SiruiLuo/CASA0022_Spectrum_Atlas/Detector/ros_catkin_ws/src/rqt/rqt_gui/resource/rqt.png

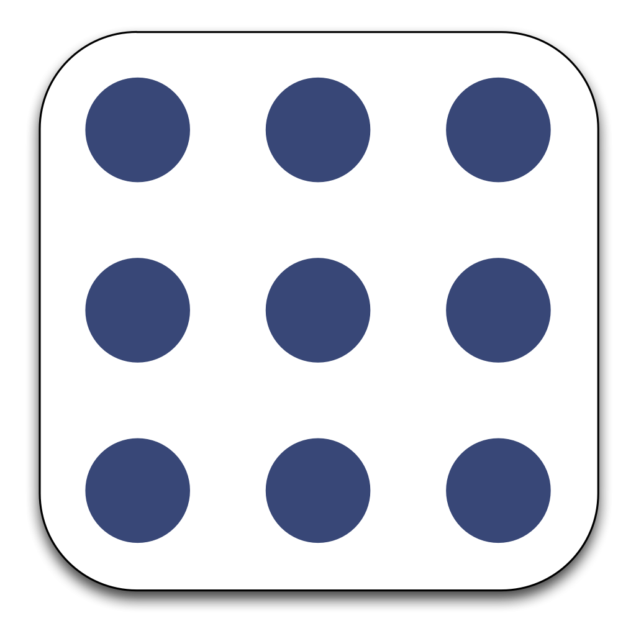
Detector/ros_catkin_ws/src/rqt/rqt_gui/resource/rqt.png
