SiruiLuo/CASA0022_Spectrum_Atlas/Detector/ros_catkin_ws/src/rqt_robot_dashboard/images/nonsvg/battery-100.png

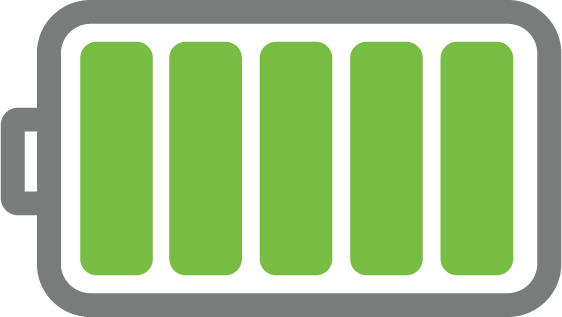
Detector/ros_catkin_ws/src/rqt_robot_dashboard/images/nonsvg/battery-100.png
