SiruiLuo/CASA0022_Spectrum_Atlas/Detector/ros_catkin_ws/src/rviz/doc/grouped-displays.png

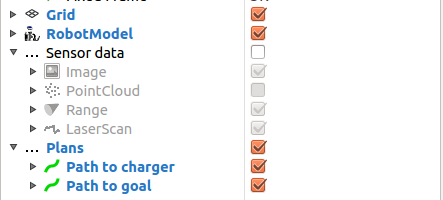
Detector/ros_catkin_ws/src/rviz/doc/grouped-displays.png
