SiruiLuo/CASA0022_Spectrum_Atlas/Detector/ros_catkin_ws/src/rviz/doc/views-panel.png

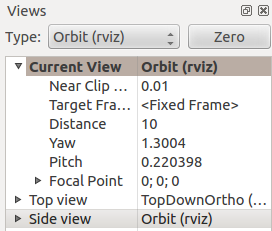
Detector/ros_catkin_ws/src/rviz/doc/views-panel.png
