SiruiLuo/CASA0022_Spectrum_Atlas/Detector/ros_catkin_ws/src/rviz/ogre_media/textures/no_image.png

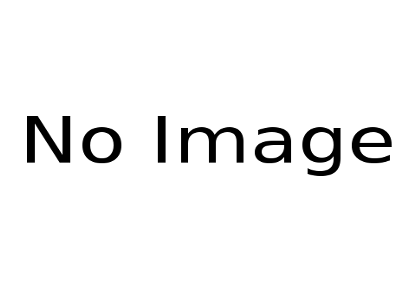
Detector/ros_catkin_ws/src/rviz/ogre_media/textures/no_image.png
