SiruiLuo/CASA0022_Spectrum_Atlas/Images/Box2.png

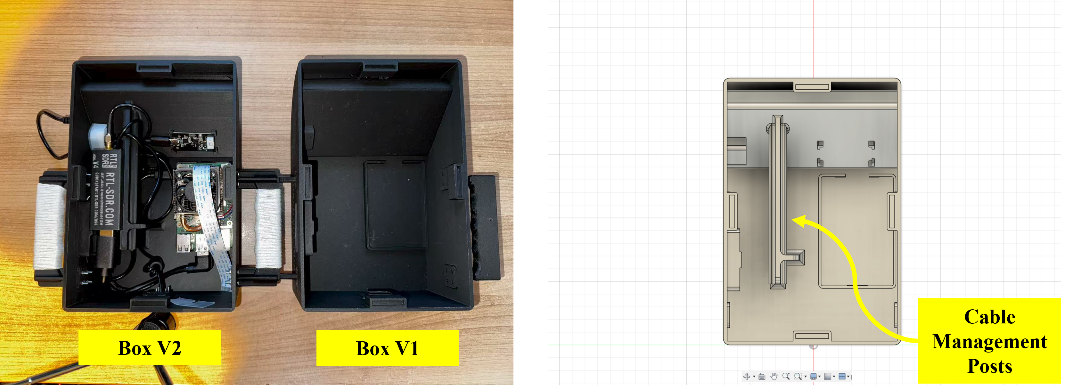
Images/Box2.png
