SiruiLuo/CASA0022_Spectrum_Atlas/Images/Cloudflare Config.png

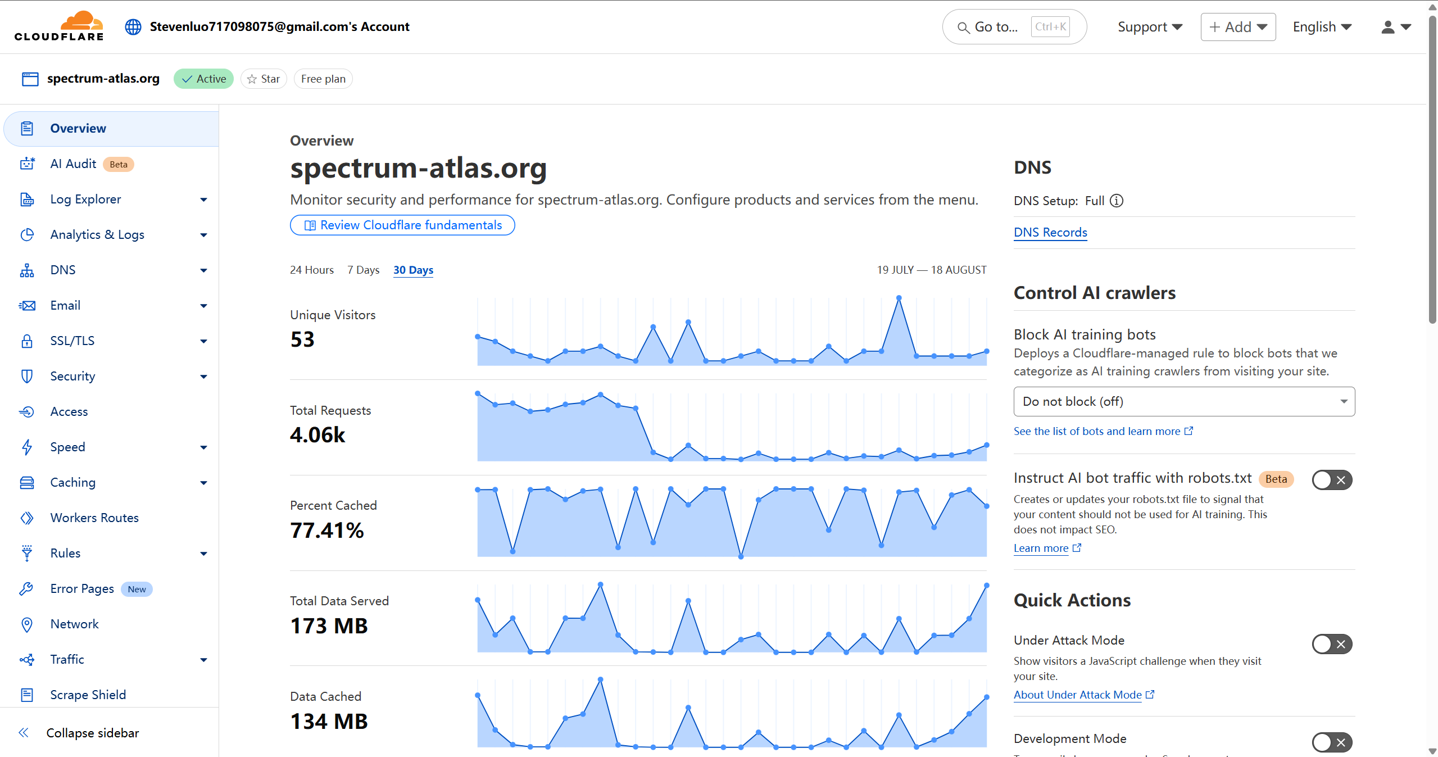
Images/Cloudflare Config.png
