SiruiLuo/CASA0022_Spectrum_Atlas/Images/Cloudflare Tunnel Settings.png

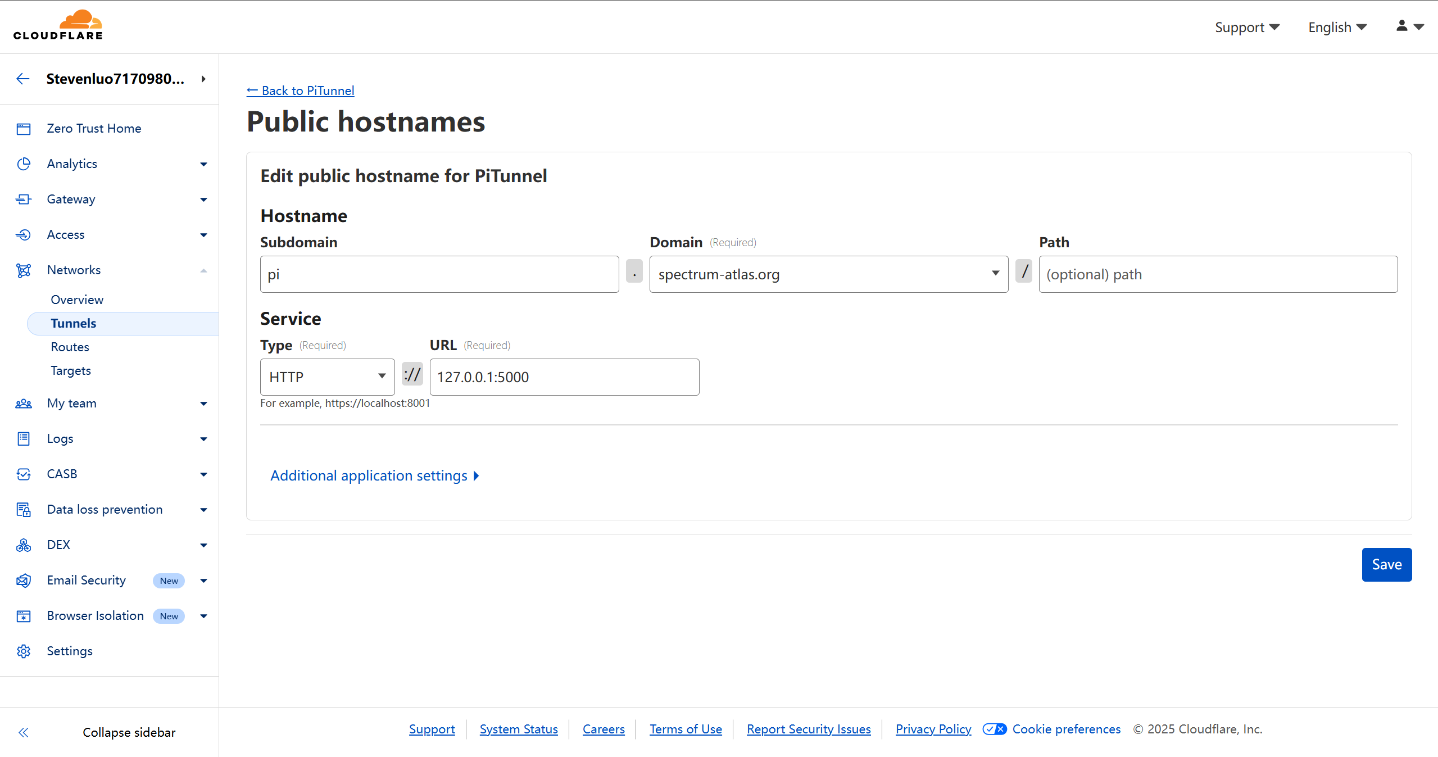
Images/Cloudflare Tunnel Settings.png
