SiruiLuo/CASA0022_Spectrum_Atlas/Images/Fan.png

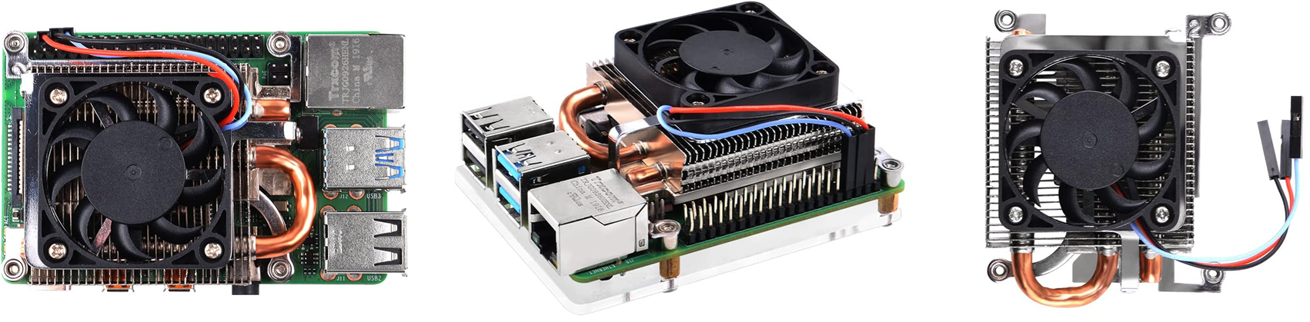
Images/Fan.png
