SiruiLuo/CASA0022_Spectrum_Atlas/Images/Flask loading.png

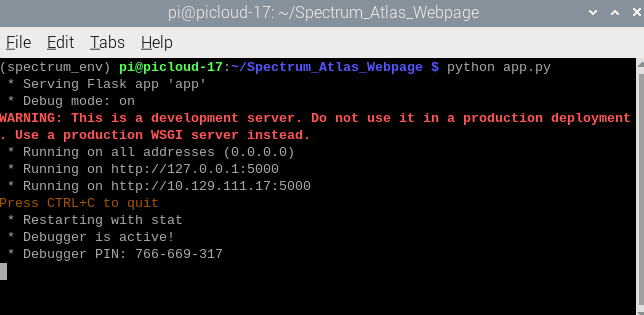
Images/Flask loading.png
