SiruiLuo/CASA0022_Spectrum_Atlas/Images/Front View.jpg

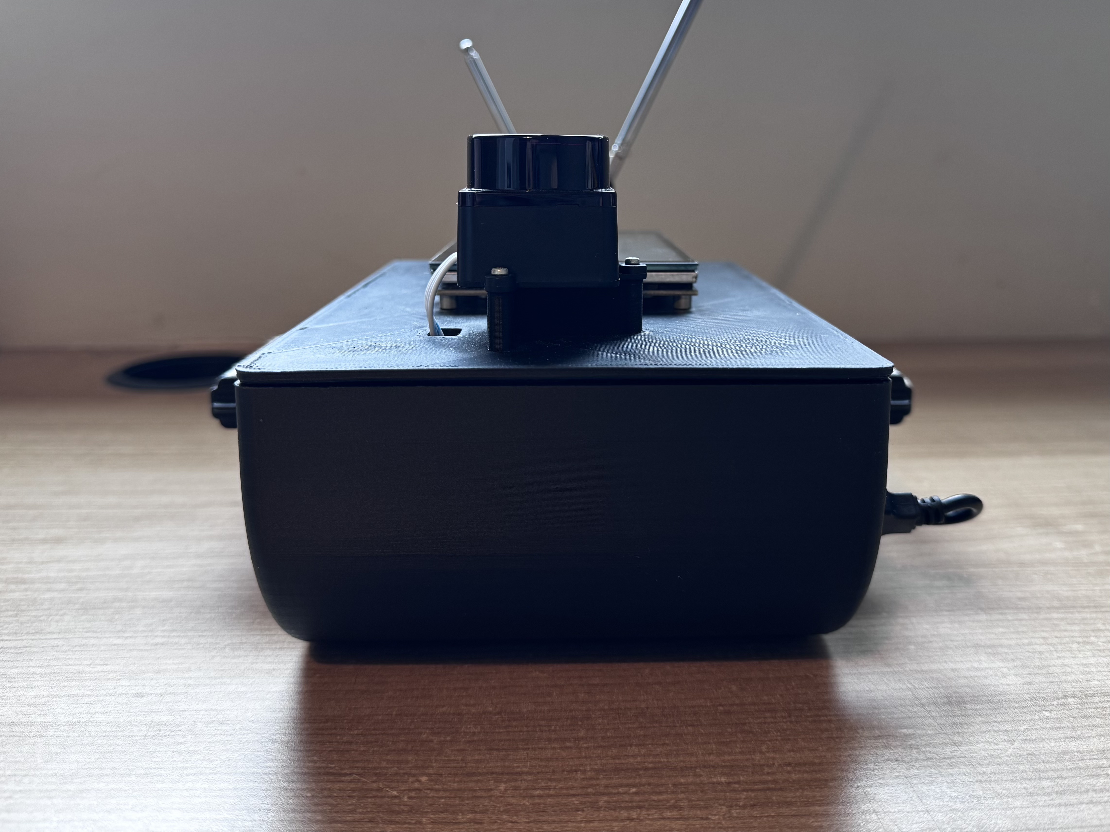
Images/Front View.jpg
