SiruiLuo/CASA0022_Spectrum_Atlas/Images/GUI flowchart.png

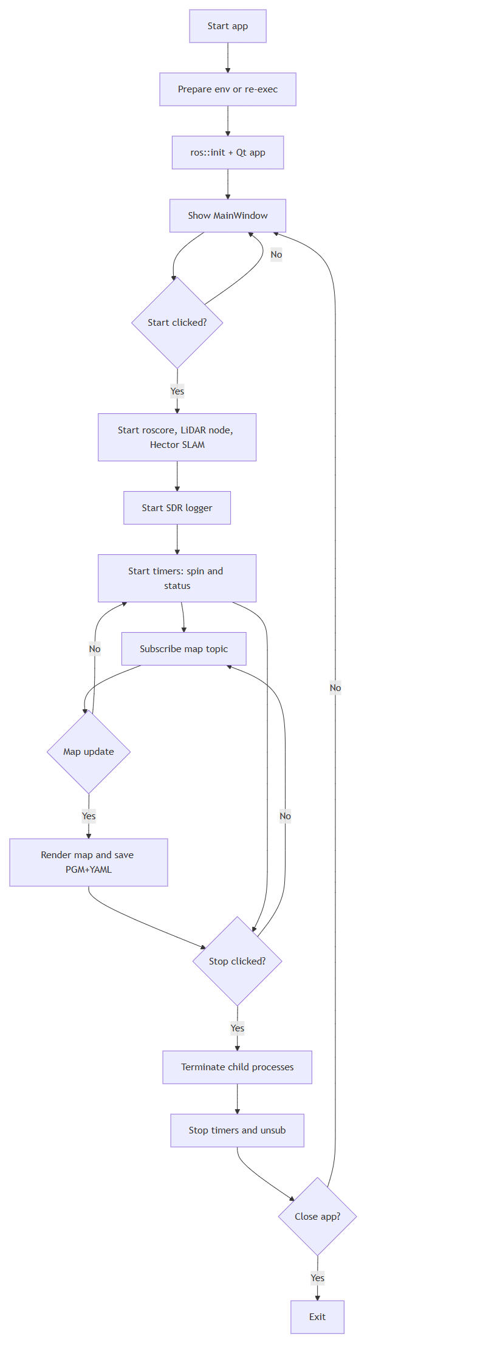
Images/GUI flowchart.png
