SiruiLuo/CASA0022_Spectrum_Atlas/Images/heatmap_ADS-B_1090_MarshgateReal_20250714_172855.png

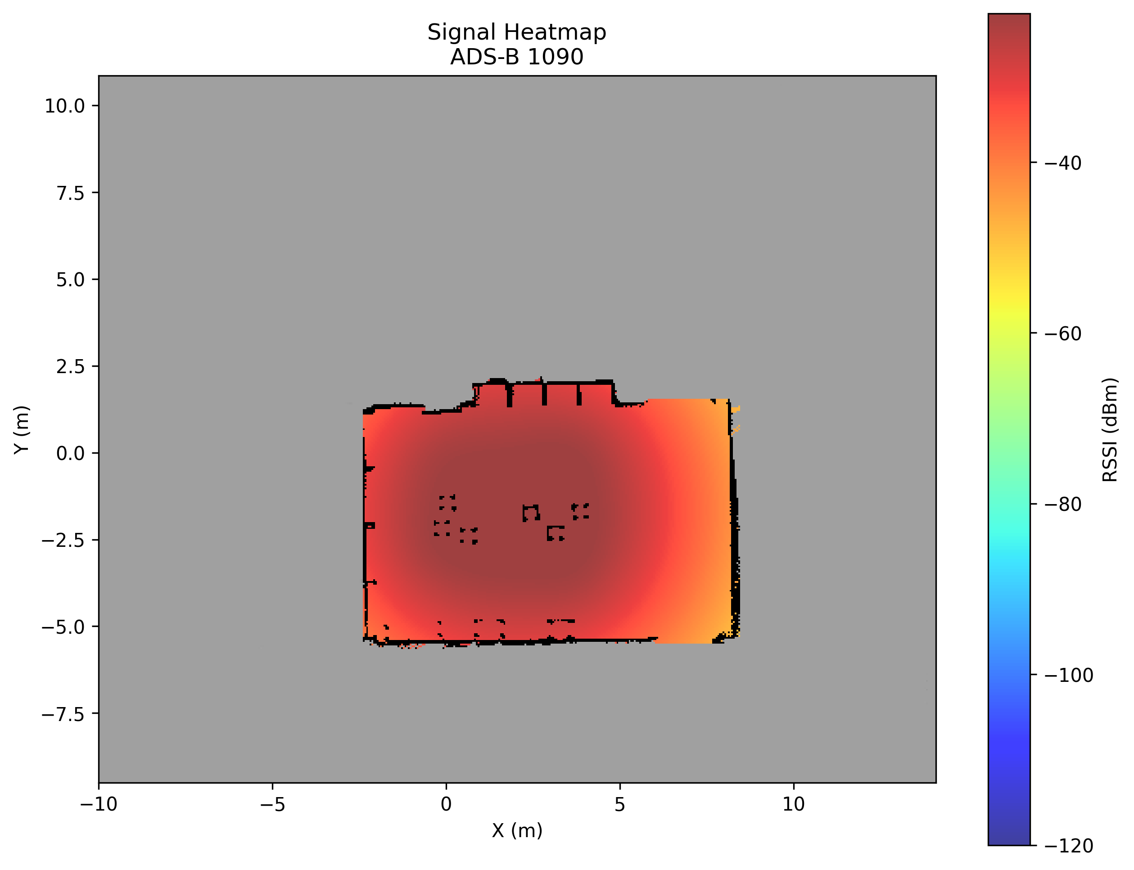
Images/heatmap_ADS-B_1090_MarshgateReal_20250714_172855.png
