SiruiLuo/CASA0022_Spectrum_Atlas/Images/Internal Overview.jpg

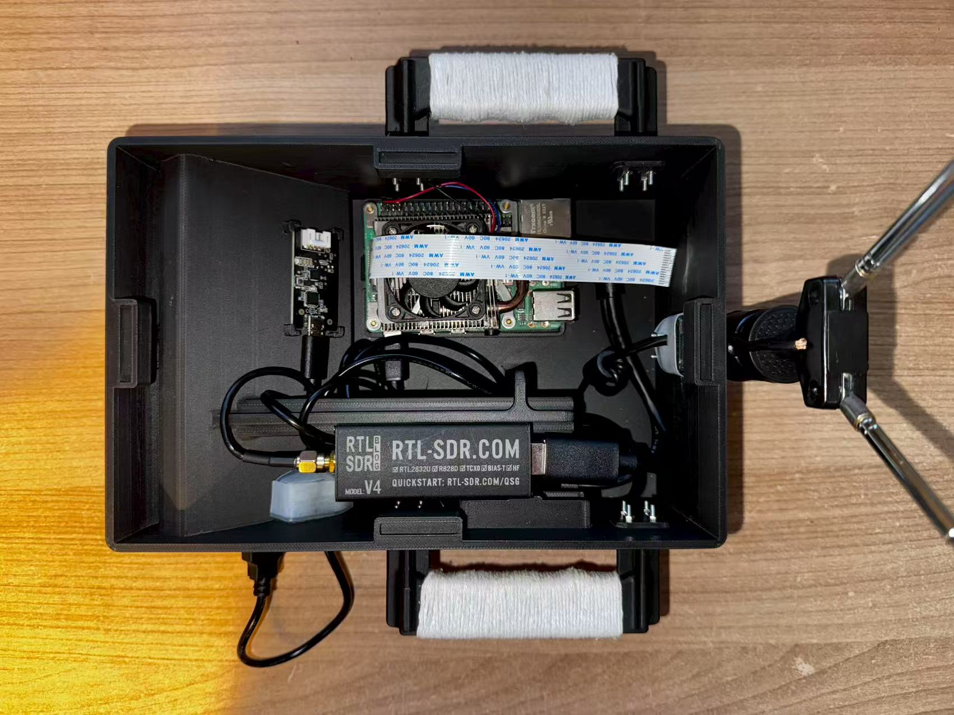
Images/Internal Overview.jpg
