SiruiLuo/CASA0022_Spectrum_Atlas/Images/LD19.png

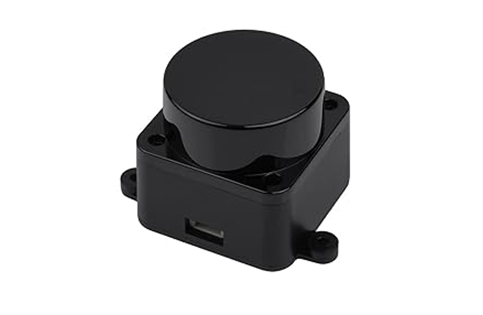
Images/LD19.png
