SiruiLuo/CASA0022_Spectrum_Atlas/Images/PostgreSQL Definition.png

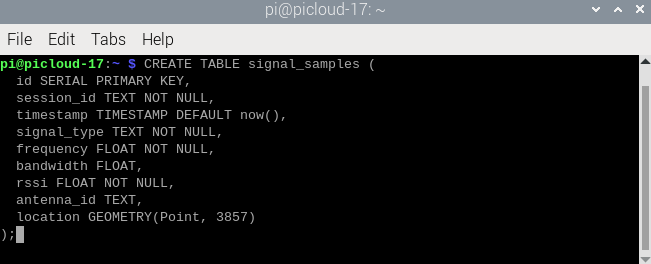
Images/PostgreSQL Definition.png
