SiruiLuo/CASA0022_Spectrum_Atlas/Images/Ringing.png

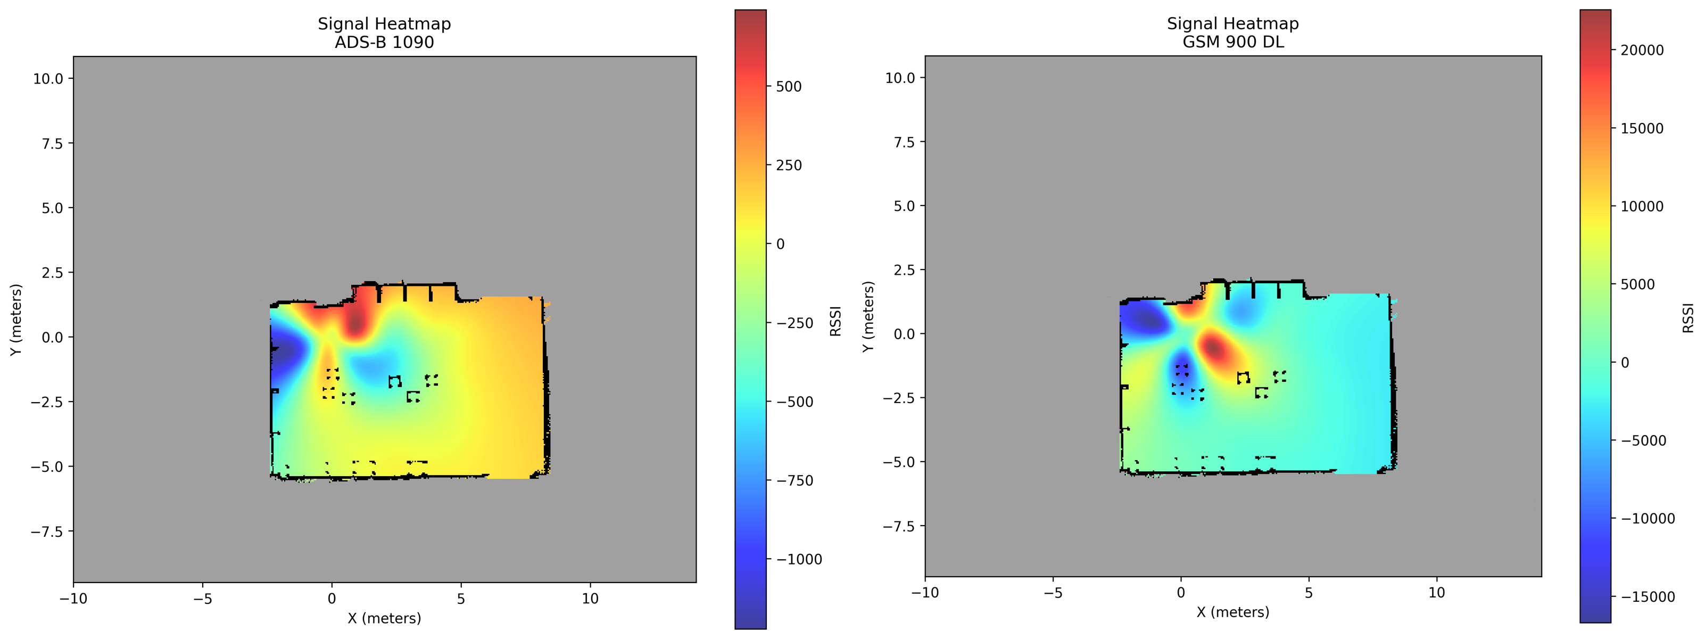
Images/Ringing.png
