SiruiLuo/CASA0022_Spectrum_Atlas/Images/RTL-SDR.png

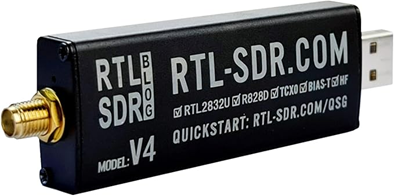
Images/RTL-SDR.png
