SiruiLuo/CASA0022_Spectrum_Atlas/Images/Side View.jpg

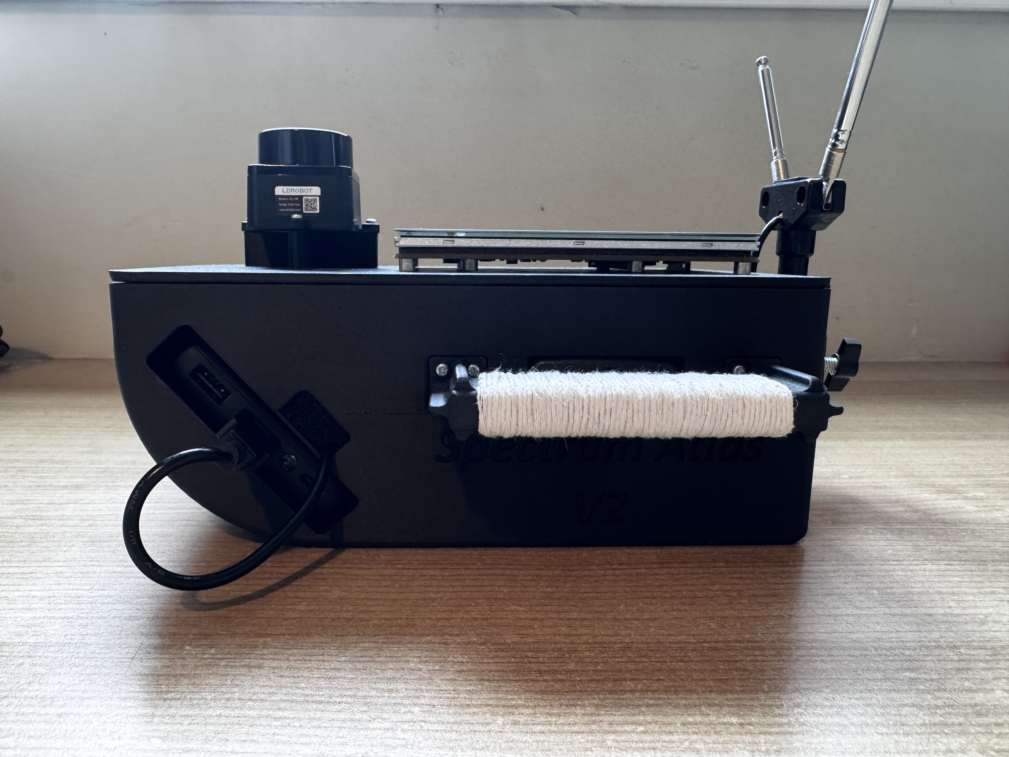
Images/Side View.jpg
