SiruiLuo/CASA0022_Spectrum_Atlas/Images/Top View.jpg

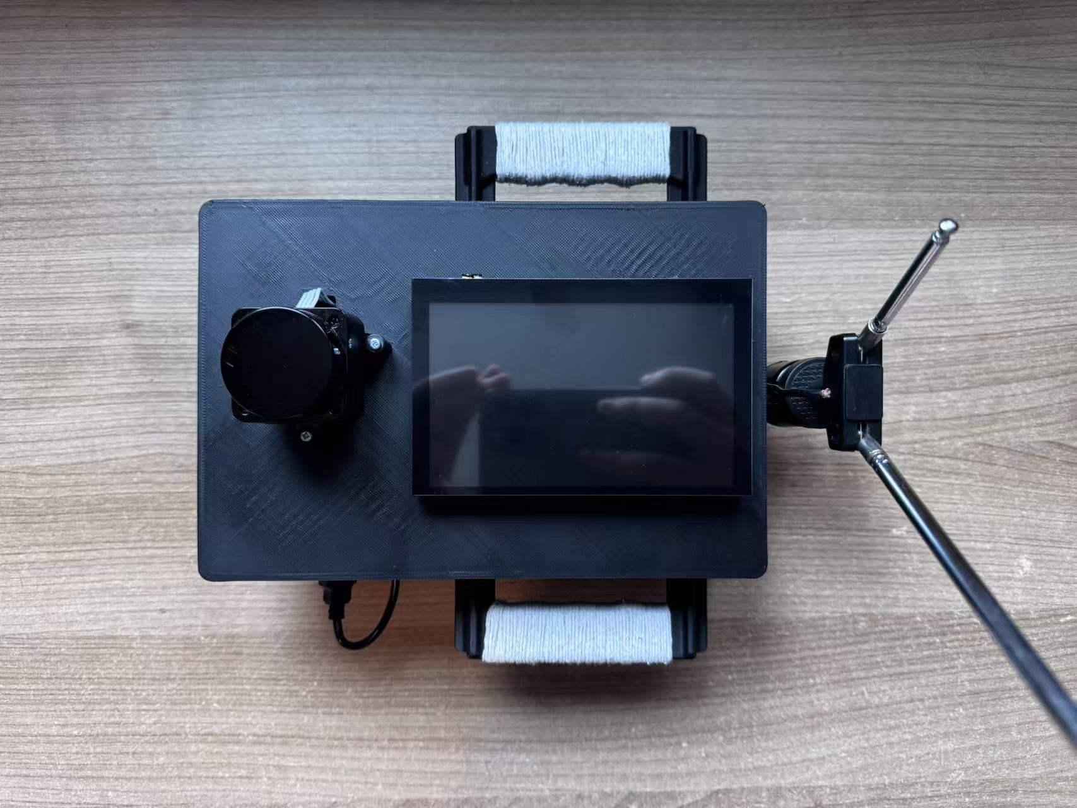
Images/Top View.jpg
