SiruiLuo/CASA0022_Spectrum_Atlas/Server and Database/Flask Server/Spectrum_Atlas_Webpage-main/pics/heat3D.png

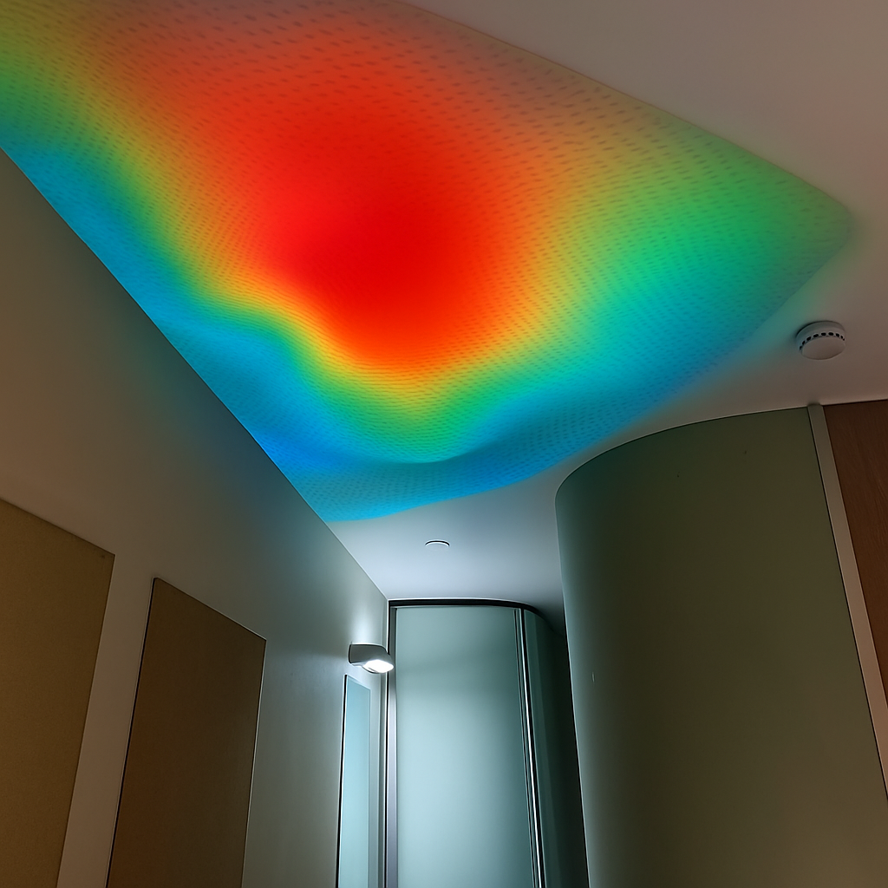
Server and Database/Flask Server/Spectrum_Atlas_Webpage-main/pics/heat3D.png
