SiruiLuo/CASA0022_Spectrum_Atlas/Server and Database/Flask Server/Spectrum_Atlas_Webpage-main/pics/Project Structure.png

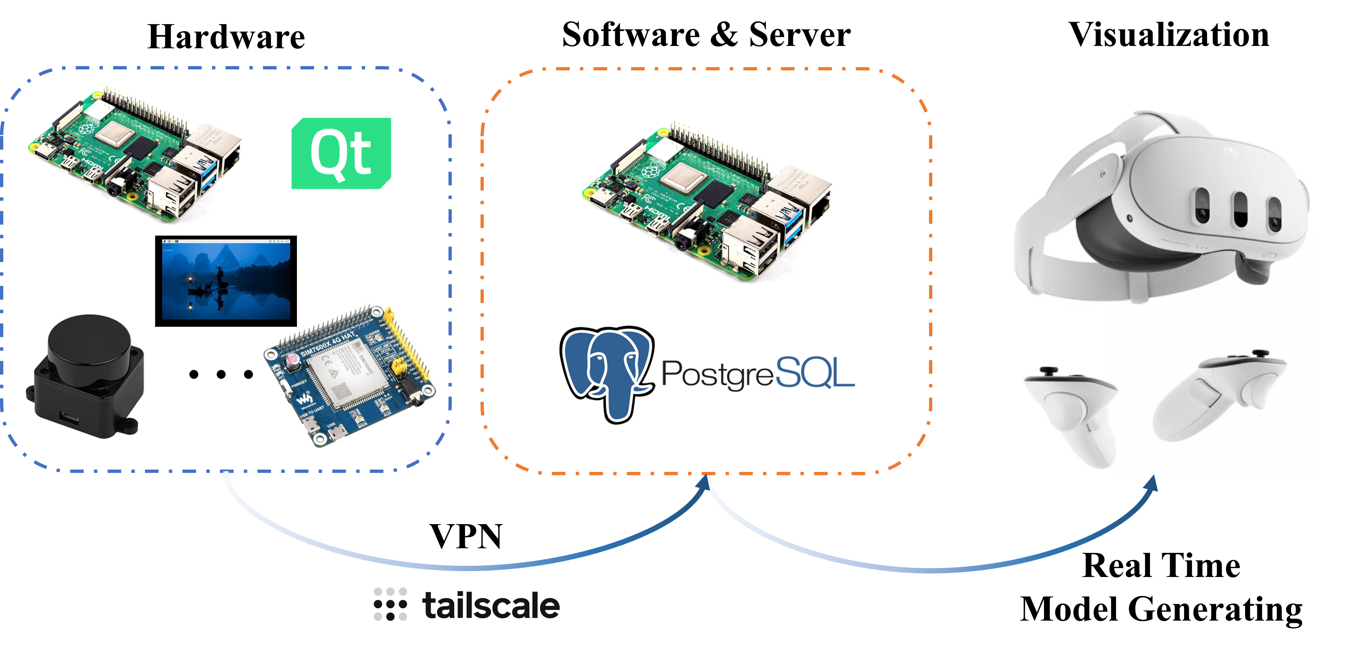
Server and Database/Flask Server/Spectrum_Atlas_Webpage-main/pics/Project Structure.png
