SiruiLuo/CASA0022_Spectrum_Atlas/Detector/ros_catkin_ws/src/urdf_tutorial/images/materials.png

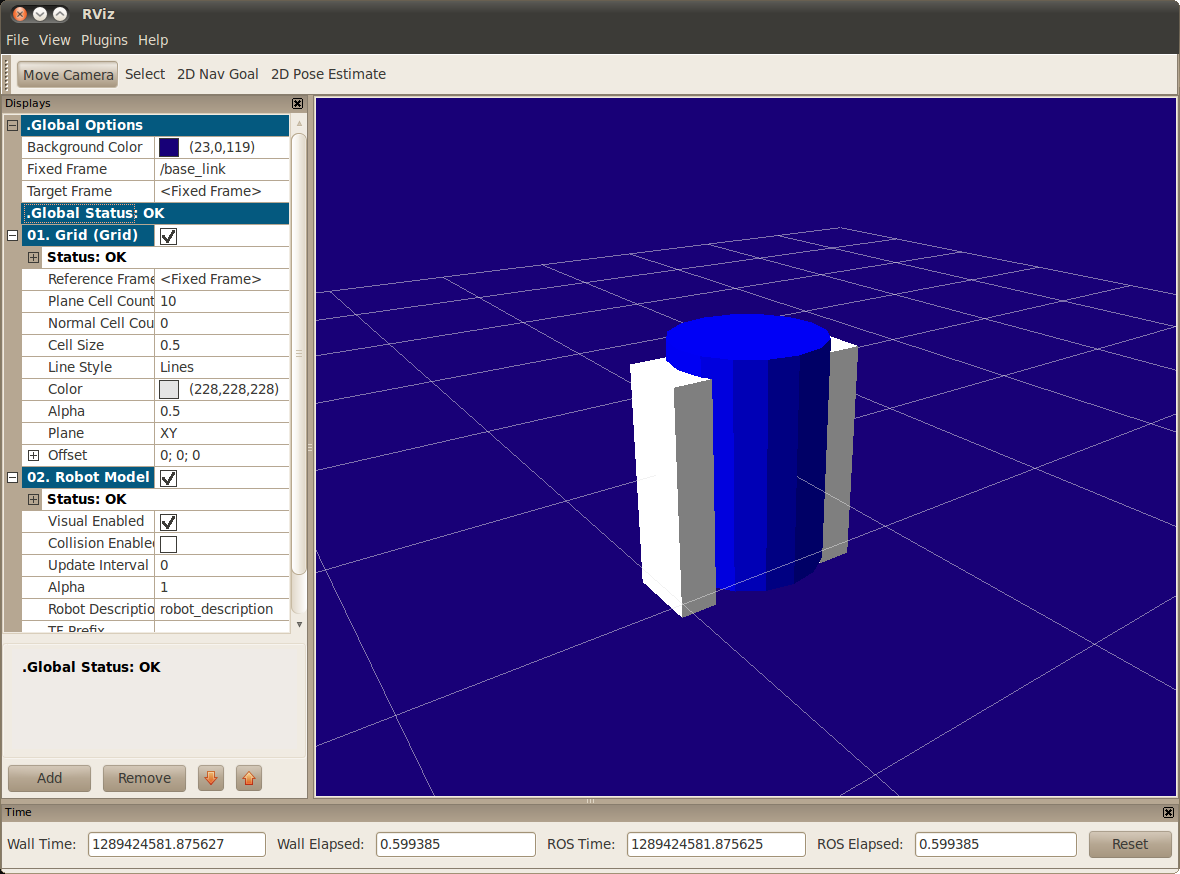
Detector/ros_catkin_ws/src/urdf_tutorial/images/materials.png
