SiruiLuo/CASA0022_Spectrum_Atlas/Detector/ros_catkin_ws/src/rviz/src/test/meshes/F10.stl

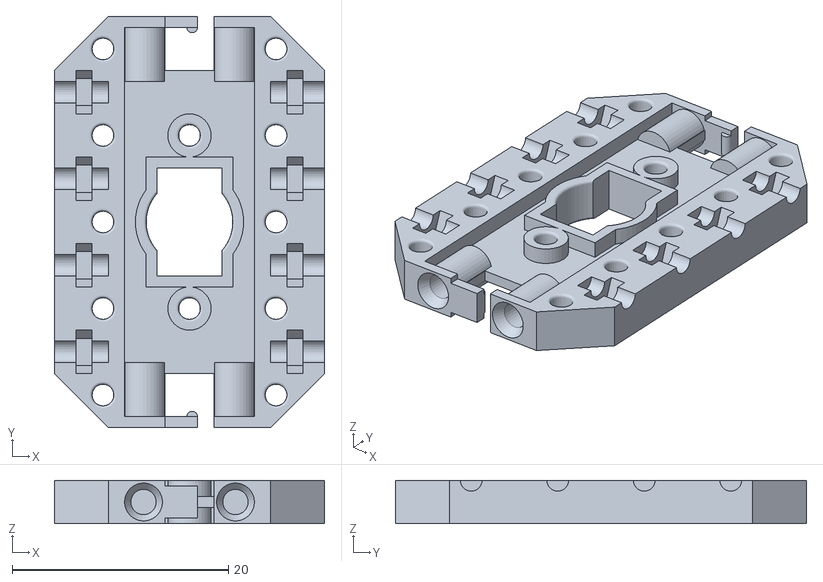
[picture p89: CAD file, 2025-08-21]
Detector/ros_catkin_ws/src/rviz/src/test/meshes/F10.stl
25.0 x 38.0 x 4.00
