SiruiLuo/CASA0022_Spectrum_Atlas/Detector/ros_catkin_ws/src/ros_tutorials/turtlesim/images/indigo.png

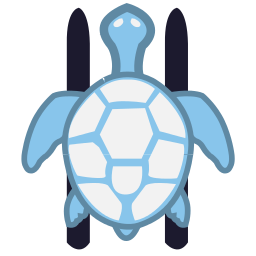
Detector/ros_catkin_ws/src/ros_tutorials/turtlesim/images/indigo.png
