SiruiLuo/CASA0022_Spectrum_Atlas/Detector/ros_catkin_ws/src/urdf_tutorial/images/flexible.png

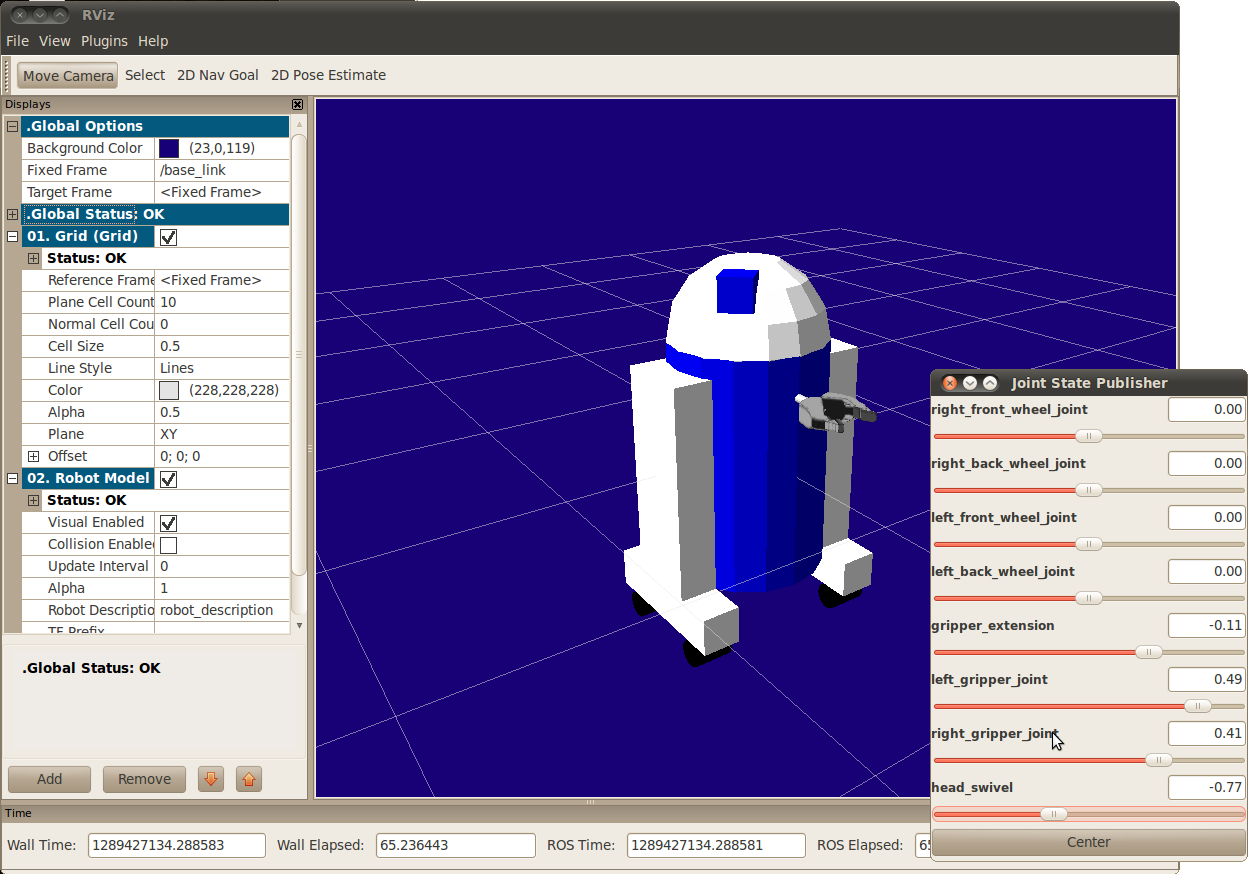
Detector/ros_catkin_ws/src/urdf_tutorial/images/flexible.png
