SiruiLuo/CASA0022_Spectrum_Atlas/Detector/ros_catkin_ws/src/visualization_tutorials/librviz_tutorial/src/doc/myviz.png

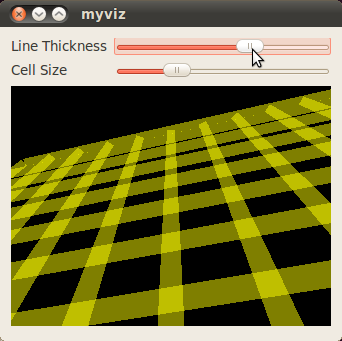
Detector/ros_catkin_ws/src/visualization_tutorials/librviz_tutorial/src/doc/myviz.png
