SiruiLuo/CASA0022_Spectrum_Atlas/Detector/ros_catkin_ws/src/visualization_tutorials/rviz_plugin_tutorials/src/doc/flags.png

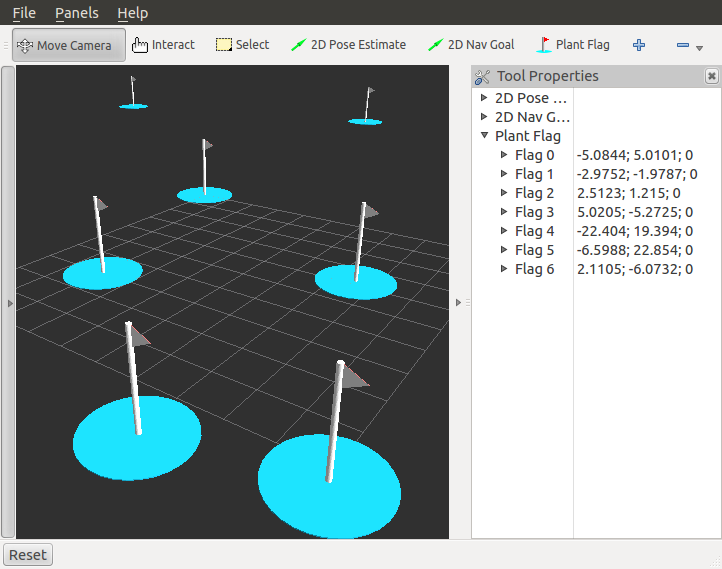
Detector/ros_catkin_ws/src/visualization_tutorials/rviz_plugin_tutorials/src/doc/flags.png
