SiruiLuo/CASA0022_Spectrum_Atlas/Detector/ros_catkin_ws/src/visualization_tutorials/rviz_python_tutorial/doc-src/myviz.png

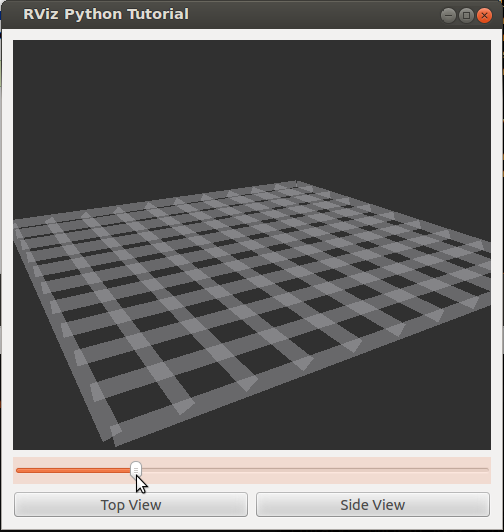
Detector/ros_catkin_ws/src/visualization_tutorials/rviz_python_tutorial/doc-src/myviz.png
