SiruiLuo/CASA0022_Spectrum_Atlas/Detector/ros_catkin_ws/src/rviz/src/test/meshes/kitchen/images/texture0.jpg

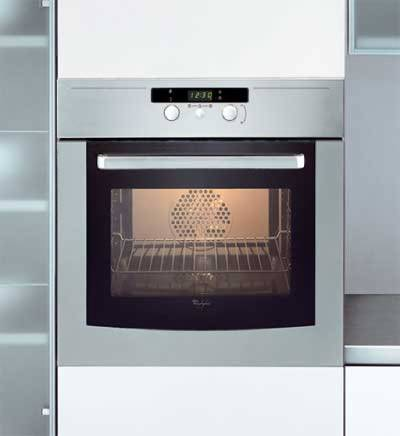
Detector/ros_catkin_ws/src/rviz/src/test/meshes/kitchen/images/texture0.jpg
