SiruiLuo/CASA0022_Spectrum_Atlas/Detector/ros_catkin_ws/src/rviz/src/test/meshes/kitchen/images/texture2.jpg

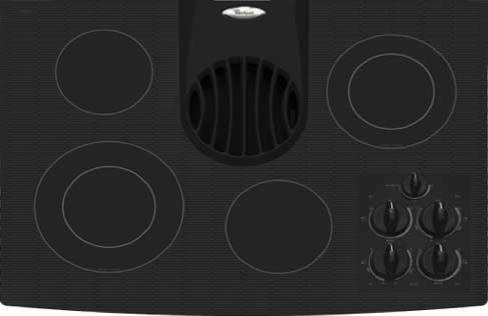
Detector/ros_catkin_ws/src/rviz/src/test/meshes/kitchen/images/texture2.jpg
